jmharvey1/ESP32BtCWKeyBrd/src/bt_keyboard.cpp

// Copyright (c) 2020 Guy Turcotte
//
// MIT License. Look at file licenses.txt for details.
//
// -----
//
// Original code from the bluetooth/esp_hid_host example of ESP-IDF license:
//
// Copyright 2017-2019 Espressif Systems (Shanghai) PTE LTD
//
// Licensed under the Apache License, Version 2.0 (the "License");
// you may not use this file except in compliance with the License.
// You may obtain a copy of the License at

//     http://www.apache.org/licenses/LICENSE-2.0
//
// Unless required by applicable law or agreed to in writing, software
// distributed under the License is distributed on an "AS IS" BASIS,
// WITHOUT WARRANTIES OR CONDITIONS OF ANY KIND, either express or implied.
// See the License for the specific language governing permissions and
// limitations under the License.
/*20230503 JMH Numerous mods to adapt the original code to work with thw ESP32 BT CW Keyboard applications*/
/*20230507 JMH reversed 'TAB & TAB+Shift Assignments to make settings screen selection move in a 'Logical' order*/
/*20230721 Fixed Crash issue related to BT Keyboard sending corrupted keystroke data; fix mostly containg bt_keyboard.hid callback code*/
/*20230810 beta fix for crash linked to 1st time connection to previously 'paired keyboard. Requires stopping ADC sampling during the 'open' Keyboard event*/
/*20230811 added bt_keyboard->Adc_Sw & bt_keyboard->OpnEvntFlg params to manage ADC sampling during connecting to a previously 'paired' keyboard*/
/*20251006 reworked keyboard pairing & reconnect */
#define __BT_KEYBOARD__ 1
#include "bt_keyboard.hpp"

#include <cstring>
#include <iostream> //JMH added
#include <stdio.h>  //JMH added
#include <string.h> //JMH added
#include "esp_hidh_api.h"  //JMH added 20251005
#define SCAN 1

// uncomment to print all devices that were seen during a scan
#define GAP_DBG_PRINTF(...) printf(__VA_ARGS__)

#define SIZEOF_ARRAY(a) (sizeof(a) / sizeof(*a))

#define WAIT_BT_CB() xSemaphoreTake(bt_hidh_cb_semaphore, portMAX_DELAY)
#define SEND_BT_CB() xSemaphoreGive(bt_hidh_cb_semaphore)

#define WAIT_BLE_CB() xSemaphoreTake(ble_hidh_cb_semaphore, portMAX_DELAY)
#define SEND_BLE_CB() xSemaphoreGive(ble_hidh_cb_semaphore)
/*JMH 20230205 - replaced the following 2 lines xSemaphoreHandle with SemaphoreHandle_t */

SemaphoreHandle_t BTKeyboard::bt_hidh_cb_semaphore = nullptr;
SemaphoreHandle_t BTKeyboard::ble_hidh_cb_semaphore = nullptr;

const char *BTKeyboard::gap_bt_prop_type_names[] = {"", "BDNAME", "COD", "RSSI", "EIR"};
//const char *BTKeyboard::ble_gap_evt_names[] = {"ADV_DATA_SET_COMPLETE", "SCAN_RSP_DATA_SET_COMPLETE", "SCAN_PARAM_SET_COMPLETE", "SCAN_RESULT", "ADV_DATA_RAW_SET_COMPLETE", "SCAN_RSP_DATA_RAW_SET_COMPLETE", "ADV_START_COMPLETE", "SCAN_START_COMPLETE", "AUTH_CMPL", "KEY", "SEC_REQ", "PASSKEY_NOTIF", "PASSKEY_REQ", "OOB_REQ", "LOCAL_IR", "LOCAL_ER", "NC_REQ", "ADV_STOP_COMPLETE", "SCAN_STOP_COMPLETE", "SET_STATIC_RAND_ADDR", "UPDATE_CONN_PARAMS", "SET_PKT_LENGTH_COMPLETE", "SET_LOCAL_PRIVACY_COMPLETE", "REMOVE_BOND_DEV_COMPLETE", "CLEAR_BOND_DEV_COMPLETE", "GET_BOND_DEV_COMPLETE", "READ_RSSI_COMPLETE", "UPDATE_WHITELIST_COMPLETE"};
//const char *BTKeyboard::bt_gap_evt_names[] = {"DISC_RES", "DISC_STATE_CHANGED", "RMT_SRVCS", "RMT_SRVC_REC", "AUTH_CMPL", "PIN_REQ", "CFM_REQ", "KEY_NOTIF", "KEY_REQ", "READ_RSSI_DELTA"};
/*20251002 JMH Revised lists */
const char *BTKeyboard::bt_gap_evt_names[] = {"BT_DISC_RES",
"BT_DISC_STATE_CHANGED",
"BT_RMT_SRVCS",
"BT_RMT_SRVC_REC",
"BT_AUTH_CMPL",
"BT_PIN_REQ",
"BT_CFM_REQ",
"BT_KEY_NOTIF",
"BT_KEY_REQ",
"BT_READ_RSSI_DELTA",
"BT_CONFIG_EIR_DATA",
"BT_SET_AFH_CHANNELS",
"BT_READ_REMOTE_NAME",
"BT_MODE_CHG",
"BT_REMOVE_BOND_DEV_COMPLETE",
"BT_QOS_CMPL",
"BT_ACL_CONN_CMPL_STAT",
"BT_ACL_DISCONN_CMPL_STAT",
"BT_SET_PAGE_TO",
"BT_GET_PAGE_TO",
"BT_ACL_PKT_TYPE_CHANGED",
"BT_ENC_CHG",
"BT_GET_DEV_NAME_CMPL",
"BT_EVT_MAX"};

const char *BTKeyboard::ble_gap_evt_names[] = {"BT_DISC_RES",
"BLE_ADV_DATA_SET_COMPLETE",
"BLE_SCAN_RSP_DATA_SET_COMPLETE",
"BLE_SCAN_PARAM_SET_COMPLETE",
"BLE_SCAN_RESULT",
"BLE_ADV_DATA_RAW_SET_COMPLETE",
"BLE_SCAN_RSP_DATA_RAW_SET_COMPLETE",
"BLE_ADV_START_COMPLETE",
"BLE_SCAN_START_COMPLETE",
"BLE_AUTH_CMPL",
"BLE_KEY",
"BLE_SEC_REQ",
"BLE_PASSKEY_NOTIF",
"BLE_PASSKEY_REQ",
"BLE_OOB_REQ",
"BLE_LOCAL_IR",
"BLE_LOCAL_ER",
"BLE_NC_REQ",
"BLE_ADV_STOP_COMPLETE",
"BLE_SCAN_STOP_COMPLETE",
"BLE_SET_STATIC_RAND_ADDR",
"BLE_UPDATE_CONN_PARAMS",
"BLE_SET_PKT_LENGTH_COMPLETE",
"BLE_SET_LOCAL_PRIVACY_COMPLETE",
"BLE_REMOVE_BOND_DEV_COMPLETE",
"BLE_CLEAR_BOND_DEV_COMPLETE",
"BLE_GET_BOND_DEV_COMPLETE",
"BLE_READ_RSSI_COMPLETE",
"BLE_UPDATE_WHITELIST_COMPLETE",
"BLE_UPDATE_DUPLICATE_EXCEPTIONAL_LIST_COMPLETE",
"BLE_SET_CHANNELS",
"BLE_READ_PHY_COMPLETE",
"BLE_SET_PREFERRED_DEFAULT_PHY_COMPLETE",
"BLE_SET_PREFERRED_PHY_COMPLETE",
"BLE_EXT_ADV_SET_RAND_ADDR_COMPLETE",
"BLE_EXT_ADV_SET_PARAMS_COMPLETE",
"BLE_EXT_ADV_DATA_SET_COMPLETE",
"BLE_EXT_SCAN_RSP_DATA_SET_COMPLETE",
"BLE_EXT_ADV_START_COMPLETE",
"BLE_EXT_ADV_STOP_COMPLETE",
"BLE_EXT_ADV_SET_REMOVE_COMPLETE",
"BLE_EXT_ADV_SET_CLEAR_COMPLETE",
"BLE_PERIODIC_ADV_SET_PARAMS_COMPLETE",
"BLE_PERIODIC_ADV_DATA_SET_COMPLETE",
"BLE_PERIODIC_ADV_START_COMPLETE",
"BLE_PERIODIC_ADV_STOP_COMPLETE",
"BLE_PERIODIC_ADV_CREATE_SYNC_COMPLETE",
"BLE_PERIODIC_ADV_SYNC_CANCEL_COMPLETE",
"BLE_PERIODIC_ADV_SYNC_TERMINATE_COMPLETE",
"BLE_PERIODIC_ADV_ADD_DEV_COMPLETE",
"BLE_PERIODIC_ADV_REMOVE_DEV_COMPLETE",
"BLE_PERIODIC_ADV_CLEAR_DEV_COMPLETE",
"BLE_SET_EXT_SCAN_PARAMS_COMPLETE",
"BLE_EXT_SCAN_START_COMPLETE",
"BLE_EXT_SCAN_STOP_COMPLETE",
"BLE_PREFER_EXT_CONN_PARAMS_SET_COMPLETE",
"BLE_PHY_UPDATE_COMPLETE",
"BLE_EXT_ADV_REPORT",
"BLE_SCAN_TIMEOUT",
"BLE_ADV_TERMINATED",
"BLE_SCAN_REQ_RECEIVED",
"BLE_CHANNEL_SELECT_ALGORITHM",
"BLE_PERIODIC_ADV_REPORT",
"BLE_PERIODIC_ADV_SYNC_LOST",
"BLE_PERIODIC_ADV_SYNC_ESTAB",
"BLE_SC_OOB_REQ",
"BLE_SC_CR_LOC_OOB",
"BLE_GET_DEV_NAME_COMPLETE",
"BLE_PERIODIC_ADV_RECV_ENABLE_COMPLETE",
"BLE_PERIODIC_ADV_SYNC_TRANS_COMPLETE",
"BLE_PERIODIC_ADV_SET_INFO_TRANS_COMPLETE",
"BLE_SET_PAST_PARAMS_COMPLETE",
"BLE_PERIODIC_ADV_SYNC_TRANS_RECV",
"BLE_DTM_TEST_UPDATE",
"BLE_ADV_CLEAR_COMPLETE",
"BLE_VENDOR_CMD_COMPLETE",
"BLE_EVT_MAX"};

const char *BTKeyboard::ble_addr_type_names[] = {"PUBLIC", "RANDOM", "RPA_PUBLIC", "RPA_RANDOM"};

const char BTKeyboard::shift_trans_dict[] =
    "aAbBcCdDeEfFgGhHiIjJkKlLmMnNoOpPqQrRsStTuUvVwWxXyYzZ1!2@3#4$5%6^7&8*9(0)"
    "\r\231\033\033\b\b\t\t  -_=+[{]}\\|??;:'\"`~,<.>/?"
    "\200\200"                                          // CAPS LOC
    "\201\201\202\202\203\203\204\204\205\205\206\206"  // F1..F6
    "\207\207\210\210\211\211\212\212\213\213\214\214"  // F7..F12
    "\215\215\216\216\217\217"                          // PrintScreen ScrollLock Pause
    "\220\220\221\221\222\222\177\177"                  // Insert Home PageUp Delete
    "\223\223\224\224\225\225\226\226\227\227\230\230"; // End PageDown Right Left Dow Up

static BTKeyboard *bt_keyboard = nullptr;
static esp_hidh_dev_t *dev = nullptr;

char msgbuf[256];

void BTKeyboard::TFTmsg(const char *msg, uint16_t color)
{
  if (bt_keyboard != nullptr)
  {
    pmsgbx->dispMsg((char *)msg, color);
  }
}
const char *
BTKeyboard::ble_addr_type_str(esp_ble_addr_type_t ble_addr_type)
{
  if (ble_addr_type > BLE_ADDR_TYPE_RPA_RANDOM)
  {
    return "UNKNOWN";
  }
  return ble_addr_type_names[ble_addr_type];
}

const char *
BTKeyboard::ble_gap_evt_str(uint8_t event)
{
  if (event >= SIZEOF_ARRAY(ble_gap_evt_names))
  {
    return "UNKNOWN";
  }
  return ble_gap_evt_names[event];
}

const char *
BTKeyboard::bt_gap_evt_str(uint8_t event)
{
  if (event >= SIZEOF_ARRAY(bt_gap_evt_names))
  {
    return "UNKNOWN";
  }
  return bt_gap_evt_names[event];
}

const char *
BTKeyboard::ble_key_type_str(esp_ble_key_type_t key_type)
{
  const char *key_str = nullptr;
  switch (key_type)
  {
  case ESP_LE_KEY_NONE:
    key_str = "ESP_LE_KEY_NONE";
    break;
  case ESP_LE_KEY_PENC:
    key_str = "ESP_LE_KEY_PENC";
    break;
  case ESP_LE_KEY_PID:
    key_str = "ESP_LE_KEY_PID";
    break;
  case ESP_LE_KEY_PCSRK:
    key_str = "ESP_LE_KEY_PCSRK";
    break;
  case ESP_LE_KEY_PLK:
    key_str = "ESP_LE_KEY_PLK";
    break;
  case ESP_LE_KEY_LLK:
    key_str = "ESP_LE_KEY_LLK";
    break;
  case ESP_LE_KEY_LENC:
    key_str = "ESP_LE_KEY_LENC";
    break;
  case ESP_LE_KEY_LID:
    key_str = "ESP_LE_KEY_LID";
    break;
  case ESP_LE_KEY_LCSRK:
    key_str = "ESP_LE_KEY_LCSRK";
    break;
  default:
    key_str = "INVALID BLE KEY TYPE";
    break;
  }

  return key_str;
}

void BTKeyboard::print_uuid(esp_bt_uuid_t *uuid)
{
  if (uuid->len == ESP_UUID_LEN_16)
  {
    GAP_DBG_PRINTF("UUID16: 0x%04x", uuid->uuid.uuid16);

    if (pDFault->DeBug)
    {
      sprintf(msgbuf, "UUID16: 0x%04x ", uuid->uuid.uuid16);
      pmsgbx->dispMsg(msgbuf, TFT_WHITE);
    }
  }
  else if (uuid->len == ESP_UUID_LEN_32)
  {
    // GAP_DBG_PRINTF("UUID32: 0x%08x", uuid->uuid.uuid32);
    /*JMH 20230205 changed to solve complie error*/
    GAP_DBG_PRINTF("UUID32: 0x%08x", (unsigned int)uuid->uuid.uuid32);
    if (pDFault->DeBug)
    {
      sprintf(msgbuf, "UUID32: 0x%08x\n", (unsigned int)uuid->uuid.uuid32);
      pmsgbx->dispMsg(msgbuf, TFT_WHITE);
    }
  }
  else if (uuid->len == ESP_UUID_LEN_128)
  {
    GAP_DBG_PRINTF("UUID128: %02x,%02x,%02x,%02x,%02x,%02x,%02x,%02x,%02x,%02x,%02x,%02x,%02x,%02x,%02x,%02x",
                   uuid->uuid.uuid128[0],
                   uuid->uuid.uuid128[1], uuid->uuid.uuid128[2], uuid->uuid.uuid128[3],
                   uuid->uuid.uuid128[4], uuid->uuid.uuid128[5], uuid->uuid.uuid128[6],
                   uuid->uuid.uuid128[7], uuid->uuid.uuid128[8], uuid->uuid.uuid128[9],
                   uuid->uuid.uuid128[10], uuid->uuid.uuid128[11], uuid->uuid.uuid128[12],
                   uuid->uuid.uuid128[13], uuid->uuid.uuid128[14], uuid->uuid.uuid128[15]);
    if (pDFault->DeBug)
    {
      sprintf(msgbuf, "\nUUID128: %02x,%02x,%02x,%02x,%02x,%02x,%02x,%02x,%02x,%02x,%02x,%02x,%02x,%02x,%02x,%02x",
              uuid->uuid.uuid128[0],
              uuid->uuid.uuid128[1], uuid->uuid.uuid128[2], uuid->uuid.uuid128[3],
              uuid->uuid.uuid128[4], uuid->uuid.uuid128[5], uuid->uuid.uuid128[6],
              uuid->uuid.uuid128[7], uuid->uuid.uuid128[8], uuid->uuid.uuid128[9],
              uuid->uuid.uuid128[10], uuid->uuid.uuid128[11], uuid->uuid.uuid128[12],
              uuid->uuid.uuid128[13], uuid->uuid.uuid128[14], uuid->uuid.uuid128[15]);
      pmsgbx->dispMsg(msgbuf, TFT_WHITE);
    }
  }
}

void BTKeyboard::esp_hid_scan_results_free(esp_hid_scan_result_t *results)
{
  esp_hid_scan_result_t *r = nullptr;
  while (results)
  {
    r = results;
    results = results->next;
    if (r->name != nullptr)
    {
      free((char *)r->name);
    }
    free(r);
  }
}

BTKeyboard::esp_hid_scan_result_t *
BTKeyboard::find_scan_result(esp_bd_addr_t bda, esp_hid_scan_result_t *results)
{
  esp_hid_scan_result_t *r = results;
  while (r)
  {
    if (memcmp(bda, r->bda, sizeof(esp_bd_addr_t)) == 0)
    {
      return r;
    }
    r = r->next;
  }
  return nullptr;
}

void BTKeyboard::add_bt_scan_result(esp_bd_addr_t bda,
                                    esp_bt_cod_t *cod,
                                    esp_bt_uuid_t *uuid,
                                    uint8_t *name,
                                    uint8_t name_len,
                                    int rssi)
{
  esp_hid_scan_result_t *r = find_scan_result(bda, bt_scan_results);
  if (r)
  {
    // Some info may come later
    if (r->name == nullptr && name && name_len)
    {
      char *name_s = (char *)malloc(name_len + 1);
      if (name_s == nullptr)
      {
        ESP_LOGE(TAG, "Malloc result name failed!");
        return;
      }
      memcpy(name_s, name, name_len);
      name_s[name_len] = 0;
      r->name = (const char *)name_s;
      printf("BT New name: %s\n", r->name); //JMH Diagnostic testing
    }
    if (r->bt.uuid.len == 0 && uuid->len)
    {
      memcpy(&r->bt.uuid, uuid, sizeof(esp_bt_uuid_t));
    }
    if (rssi != 0)
    {
      r->rssi = rssi;
    }
    return;
  }

  r = (esp_hid_scan_result_t *)malloc(sizeof(esp_hid_scan_result_t));

  if (r == nullptr)
  {
    ESP_LOGE(TAG, "Malloc bt_hidh_scan_result_t failed!");
    if (pDFault->DeBug)
    {
      sprintf(msgbuf, "Malloc bt_hidh_scan_result_t failed!\n");
      pmsgbx->dispMsg(msgbuf, TFT_RED);
    }
    return;
  }

  r->transport = ESP_HID_TRANSPORT_BT;

  memcpy(r->bda, bda, sizeof(esp_bd_addr_t));
  memcpy(&r->bt.cod, cod, sizeof(esp_bt_cod_t));
  memcpy(&r->bt.uuid, uuid, sizeof(esp_bt_uuid_t));

  r->usage = esp_hid_usage_from_cod((uint32_t)cod);
  r->rssi = rssi;
  r->name = nullptr;

  if (name_len && name)
  {
    char *name_s = (char *)malloc(name_len + 1);
    if (name_s == nullptr)
    {
      free(r);
      ESP_LOGE(TAG, "Malloc result name failed!");
      if (pDFault->DeBug)
      {
        sprintf(msgbuf, "Malloc result name failed!\n");
        pmsgbx->dispMsg(msgbuf, TFT_RED);
      }
      return;
    }
    memcpy(name_s, name, name_len);
    name_s[name_len] = 0;
    r->name = (const char *)name_s;
  }
  r->next = bt_scan_results;
  bt_scan_results = r;
  num_bt_scan_results++;
}

void BTKeyboard::add_ble_scan_result(esp_bd_addr_t bda,
                                     esp_ble_addr_type_t addr_type,
                                     uint16_t appearance,
                                     uint8_t *name,
                                     uint8_t name_len,
                                     int rssi)
{
  if (find_scan_result(bda, ble_scan_results))
  {
    ESP_LOGW(TAG, "Result already exists!");
    if (pDFault->DeBug)
    {
      sprintf(msgbuf, "Result already exists!\n");
      pmsgbx->dispMsg(msgbuf, TFT_YELLOW);
    }
    return;
  }

  esp_hid_scan_result_t *r = (esp_hid_scan_result_t *)malloc(sizeof(esp_hid_scan_result_t));

  if (r == nullptr)
  {
    ESP_LOGE(TAG, "Malloc ble_hidh_scan_result_t failed!");
    if (pDFault->DeBug)
    {
      sprintf(msgbuf, "Malloc ble_hidh_scan_result_t failed!\n");
      pmsgbx->dispMsg(msgbuf, TFT_RED);
    }
    return;
  }

  r->transport = ESP_HID_TRANSPORT_BLE;

  memcpy(r->bda, bda, sizeof(esp_bd_addr_t));

  r->ble.appearance = appearance;
  r->ble.addr_type = addr_type;
  r->usage = esp_hid_usage_from_appearance(appearance);
  r->rssi = rssi;
  r->name = nullptr;

  if (name_len && name)
  {
    char *name_s = (char *)malloc(name_len + 1);
    if (name_s == nullptr)
    {
      free(r);
      ESP_LOGE(TAG, "Malloc result name failed!");
      if (pDFault->DeBug)
      {
        sprintf(msgbuf, "Malloc result name failed!\n");
        pmsgbx->dispMsg(msgbuf, TFT_RED);
      }
      return;
    }
    memcpy(name_s, name, name_len);
    name_s[name_len] = 0;
    r->name = (const char *)name_s;
    printf("BLE New name: %s\n", r->name); //JMH Diagnostic testing
  }

  r->next = ble_scan_results;
  ble_scan_results = r;
  num_ble_scan_results++;
}

bool BTKeyboard::setup(pid_handler *handler)
{
  esp_err_t ret;
  const esp_bt_mode_t mode = HID_HOST_MODE;

  if (bt_keyboard != nullptr)
  {
    ESP_LOGE(TAG, "Setup called more than once. Only one instance of BTKeyboard is allowed.");
    if (pDFault->DeBug)
    {
      sprintf(msgbuf, "Setup called more than once. Only one instance of BTKeyboard is allowed.\n");
      pmsgbx->dispMsg(msgbuf, TFT_YELLOW);
    }
    return false;
  }

  bt_keyboard = this;

  pairing_handler = handler;
  event_queue = xQueueCreate(10, sizeof(KeyInfo));

  if (HID_HOST_MODE == HIDH_IDLE_MODE)
  {
    ESP_LOGE(TAG, "Please turn on BT HID host or BLE!");
    sprintf(msgbuf, "Please turn on BT HID host or BLE!\n");
    pmsgbx->dispStat(msgbuf, TFT_YELLOW);
    return false;
  }

  bt_hidh_cb_semaphore = xSemaphoreCreateBinary();
  if (bt_hidh_cb_semaphore == nullptr)
  {
    ESP_LOGE(TAG, "xSemaphoreCreateMutex failed!");
    sprintf(msgbuf, "xSemaphoreCreateMutex failed!\n");
    pmsgbx->dispStat(msgbuf, TFT_RED);
    return false;
  }

  ble_hidh_cb_semaphore = xSemaphoreCreateBinary();
  if (ble_hidh_cb_semaphore == nullptr)
  {
    ESP_LOGE(TAG, "xSemaphoreCreateMutex failed!");
    sprintf(msgbuf, "xSemaphoreCreateMutex failed!\n");
    pmsgbx->dispStat(msgbuf, TFT_RED);
    vSemaphoreDelete(bt_hidh_cb_semaphore);
    bt_hidh_cb_semaphore = nullptr;
    return false;
  }

  esp_bt_controller_config_t bt_cfg = BT_CONTROLLER_INIT_CONFIG_DEFAULT();

  bt_cfg.mode = mode;
  bt_cfg.bt_max_acl_conn = 3;
  bt_cfg.bt_max_sync_conn = 3;

  if ((ret = esp_bt_controller_init(&bt_cfg)))
  {
    ESP_LOGE(TAG, "esp_bt_controller_init failed: %d", ret);
    sprintf(msgbuf, "esp_bt_controller_init failed: %d\n", ret);
    pmsgbx->dispStat(msgbuf, TFT_YELLOW);
    return false;
  }

  if ((ret = esp_bt_controller_enable(mode)))
  {
    ESP_LOGE(TAG, "esp_bt_controller_enable failed: %d", ret);
    sprintf(msgbuf, "esp_bt_controller_enable failed: %d\n", ret);
    pmsgbx->dispStat(msgbuf, TFT_YELLOW);
    return false;
  }

  if ((ret = esp_bluedroid_init()))
  {
    ESP_LOGE(TAG, "esp_bluedroid_init failed: %d", ret);
    sprintf(msgbuf, "esp_bluedroid_init failed: %d\n", ret);
    pmsgbx->dispStat(msgbuf, TFT_YELLOW);
    return false;
  }

  if ((ret = esp_bluedroid_enable()))
  {
    ESP_LOGE(TAG, "esp_bluedroid_enable failed: %d", ret);
    sprintf(msgbuf, "esp_bluedroid_enable failed: %d\n", ret);
    pmsgbx->dispStat(msgbuf, TFT_YELLOW);
    return false;
  }

  // Classic Bluetooth GAP

  esp_bt_sp_param_t param_type = ESP_BT_SP_IOCAP_MODE;
  //esp_bt_io_cap_t iocap = ESP_BT_IO_CAP_IO;
  esp_bt_gap_set_security_param(param_type, &iocap, sizeof(uint8_t));

  /*
   * Set default parameters for Legacy Pairing
   * Use variable pin, input pin code when pairing
   */
  esp_bt_pin_type_t pin_type = ESP_BT_PIN_TYPE_VARIABLE;
  esp_bt_pin_code_t pin_code;
  esp_bt_gap_set_pin(pin_type, 0, pin_code);

  if ((ret = esp_bt_gap_register_callback(bt_gap_event_handler)))
  {
    ESP_LOGE(TAG, "esp_bt_gap_register_callback failed: %d", ret);
    sprintf(msgbuf, "esp_bt_gap_register_callback failed: %d\n", ret);
    pmsgbx->dispStat(msgbuf, TFT_YELLOW);
    return false;
  }

  // Allow BT devices to connect back to us
  if ((ret = esp_bt_gap_set_scan_mode(ESP_BT_CONNECTABLE, ESP_BT_NON_DISCOVERABLE)))
  {
    ESP_LOGE(TAG, "esp_bt_gap_set_scan_mode failed: %d", ret);
    sprintf(msgbuf, "esp_bt_gap_set_scan_mode failed: %d\n", ret);
    pmsgbx->dispStat(msgbuf, TFT_YELLOW);
    return false;
  }

  // BLE GAP

  if ((ret = esp_ble_gap_register_callback(ble_gap_event_handler)))
  {
    ESP_LOGE(TAG, "esp_ble_gap_register_callback failed: %d", ret);
    sprintf(msgbuf, "esp_bt_gap_set_scan_mode ffailed: %d\n", ret);
    pmsgbx->dispStat(msgbuf, TFT_YELLOW);
    return false;
  }

  ESP_ERROR_CHECK(esp_ble_gattc_register_callback(esp_hidh_gattc_event_handler));
  esp_hidh_config_t config = {
      .callback = hidh_callback,
      .event_stack_size = 4 * 1024, // Required with ESP-IDF 4.4
      .callback_arg = nullptr       // idem
  };
  ESP_ERROR_CHECK(esp_hidh_init(&config));

  for (int i = 0; i < MAX_KEY_COUNT; i++)
  {
    key_avail[i] = true;
  }
  last_ch = 0;
  battery_level = -1;
  return true;
}

void BTKeyboard::handle_bt_device_result(esp_bt_gap_cb_param_t *param)
{
  GAP_DBG_PRINTF("BT : " ESP_BD_ADDR_STR, ESP_BD_ADDR_HEX(param->disc_res.bda));
  if (pDFault->DeBug)
  {
    sprintf(msgbuf, "BT  %02x:%02x:%02x:%02x:%02x:%02x", ESP_BD_ADDR_HEX(param->disc_res.bda));
    pmsgbx->dispMsg(msgbuf, TFT_WHITE);
  }
  uint32_t codv = 0;
  esp_bt_cod_t *cod = (esp_bt_cod_t *)&codv;
  int8_t rssi = 0;
  uint8_t *name = nullptr;
  uint8_t name_len = 0;
  esp_bt_uuid_t uuid;

  uuid.len = ESP_UUID_LEN_16;
  uuid.uuid.uuid16 = 0;

  for (int i = 0; i < param->disc_res.num_prop; i++)
  {
    esp_bt_gap_dev_prop_t *prop = &param->disc_res.prop[i];
    if (prop->type != ESP_BT_GAP_DEV_PROP_EIR)
    {
      GAP_DBG_PRINTF(", %s: ", gap_bt_prop_type_names[prop->type]);
      // if (pDFault->DeBug)
      // {
      //   sprintf(msgbuf, ", %s: ", gap_bt_prop_type_names[prop->type]);
      //   pmsgbx->dispMsg(msgbuf, TFT_WHITE);
      // }
    }
    if (prop->type == ESP_BT_GAP_DEV_PROP_BDNAME)
    {
      name = (uint8_t *)prop->val;
      name_len = strlen((const char *)name);
      GAP_DBG_PRINTF("%s", (const char *)name);
      if (pDFault->DeBug)
      {
        sprintf(msgbuf, "%s", (const char *)name);
        pmsgbx->dispMsg(msgbuf, TFT_WHITE);
      }
    }
    else if (prop->type == ESP_BT_GAP_DEV_PROP_RSSI)
    {
      rssi = *((int8_t *)prop->val);
      GAP_DBG_PRINTF("%d", rssi);
      // if (pDFault->DeBug)
      // {
      //   sprintf(msgbuf, "%d", rssi);
      //   pmsgbx->dispMsg(msgbuf, TFT_WHITE);
      // }
    }
    else if (prop->type == ESP_BT_GAP_DEV_PROP_COD)
    {
      memcpy(&codv, prop->val, sizeof(uint32_t));
      GAP_DBG_PRINTF("major: %s, minor: %d, service: 0x%03x", esp_hid_cod_major_str(cod->major), cod->minor, cod->service);
      // if (pDFault->DeBug)
      // {
      //   sprintf(msgbuf, "major: %s, minor: %d, service: 0x%03x", esp_hid_cod_major_str(cod->major), cod->minor, cod->service);
      //   pmsgbx->dispMsg(msgbuf, TFT_WHITE);
      // }
    }
    else if (prop->type == ESP_BT_GAP_DEV_PROP_EIR)
    {
      uint8_t len = 0;
      uint8_t *data = 0;

      data = esp_bt_gap_resolve_eir_data((uint8_t *)prop->val, ESP_BT_EIR_TYPE_CMPL_16BITS_UUID, &len);

      if (data == nullptr)
      {
        data = esp_bt_gap_resolve_eir_data((uint8_t *)prop->val, ESP_BT_EIR_TYPE_INCMPL_16BITS_UUID, &len);
      }

      if (data && len == ESP_UUID_LEN_16)
      {
        uuid.len = ESP_UUID_LEN_16;
        uuid.uuid.uuid16 = data[0] + (data[1] << 8);
        GAP_DBG_PRINTF(", ");
        print_uuid(&uuid);
        continue;
      }

      data = esp_bt_gap_resolve_eir_data((uint8_t *)prop->val, ESP_BT_EIR_TYPE_CMPL_32BITS_UUID, &len);

      if (data == nullptr)
      {
        data = esp_bt_gap_resolve_eir_data((uint8_t *)prop->val, ESP_BT_EIR_TYPE_INCMPL_32BITS_UUID, &len);
      }

      if (data && len == ESP_UUID_LEN_32)
      {
        uuid.len = len;
        memcpy(&uuid.uuid.uuid32, data, sizeof(uint32_t));
        GAP_DBG_PRINTF(", ");
        print_uuid(&uuid);
        continue;
      }

      data = esp_bt_gap_resolve_eir_data((uint8_t *)prop->val, ESP_BT_EIR_TYPE_CMPL_128BITS_UUID, &len);

      if (data == nullptr)
      {
        data = esp_bt_gap_resolve_eir_data((uint8_t *)prop->val, ESP_BT_EIR_TYPE_INCMPL_128BITS_UUID, &len);
      }

      if (data && len == ESP_UUID_LEN_128)
      {
        uuid.len = len;
        memcpy(uuid.uuid.uuid128, (uint8_t *)data, len);
        GAP_DBG_PRINTF(", ");
        print_uuid(&uuid);
        continue;
      }

      // try to find a name
      if (name == nullptr)
      {
        data = esp_bt_gap_resolve_eir_data((uint8_t *)prop->val, ESP_BT_EIR_TYPE_CMPL_LOCAL_NAME, &len);

        if (data == nullptr)
        {
          data = esp_bt_gap_resolve_eir_data((uint8_t *)prop->val, ESP_BT_EIR_TYPE_SHORT_LOCAL_NAME, &len);
        }

        if (data && len)
        {
          name = data;
          name_len = len;
          GAP_DBG_PRINTF(", NAME: ");
          if (pDFault->DeBug)
          {
            sprintf(msgbuf, ", ");
            for (int x = 0; x < len; x++)
            {
              GAP_DBG_PRINTF("%c", (char)data[x]);
              /*inspite of the given lenght, treat every entry as if it were one & terminate the array with LF & 0*/
              msgbuf[2 + x] = (char)data[x];
              // msgbuf[2 + x + 1] = 0xA; // lf
              // msgbuf[2 + x + 2] = 0;
              msgbuf[2 + x + 1] = 0;
            }
            pmsgbx->dispMsg(msgbuf, TFT_WHITE);
          }
        }
      }
    }
  }
  GAP_DBG_PRINTF("\n");
  if (pDFault->DeBug)
  {
    sprintf(msgbuf, "\n");
    pmsgbx->dispMsg(msgbuf, TFT_WHITE);
  }

  if ((cod->major == ESP_BT_COD_MAJOR_DEV_PERIPHERAL) ||
      (find_scan_result(param->disc_res.bda, bt_scan_results) != nullptr))
  {
    add_bt_scan_result(param->disc_res.bda, cod, &uuid, name, name_len, rssi);
  }
}

void BTKeyboard::bt_gap_event_handler(esp_bt_gap_cb_event_t event, esp_bt_gap_cb_param_t *param)
{
  static const char *TAG1 = "bt_gap_event_handler";
  GAP_DBG_PRINTF("\tBT GAP EVT: (%d) %s\n", event, bt_gap_evt_str(event));
  switch (event)
  {
    
  case ESP_BT_GAP_DISC_STATE_CHANGED_EVT:
  {
    ESP_LOGV(TAG, "BT GAP DISC_STATE %s", (param->disc_st_chg.state == ESP_BT_GAP_DISCOVERY_STARTED) ? "START" : "STOP");
    // if(pDFault->DeBug){
    //sprintf(msgbuf, "BT GAP DISC_STATE %s", (param->disc_st_chg.state == ESP_BT_GAP_DISCOVERY_STARTED) ? "START" : "STOP"); //JMH Diagnosstic testing
    //   pmsgbx->dispMsg(msgbuf,TFT_WHITE);
    // }
    if (param->disc_st_chg.state == ESP_BT_GAP_DISCOVERY_STOPPED)
    {
      SEND_BT_CB();
    }
    break;
  }
  case ESP_BT_GAP_DISC_RES_EVT:
  {
    bt_keyboard->handle_bt_device_result(param);
    break;
  }
  case ESP_BT_GAP_AUTH_CMPL_EVT:                         /*!< Authentication complete indication */
  {
    if (param->auth_cmpl.stat == ESP_BT_STATUS_SUCCESS)
    {
      ESP_LOGI(TAG, "BT GAP AUTH_CMPL name:%s", param->auth_cmpl.device_name);
      // if(pDFault->DeBug){
      // sprintf(msgbuf, "BT GAP AUTH_CMPL name:%s", param->auth_cmpl.device_name); //JMH Diagnosstic testing
      // printf("bt_gap_event_handler: %s \n",msgbuf); //JMH Diagnosstic testing
      //   pmsgbx->dispMsg(msgbuf,TFT_WHITE);
      // }
      ESP_LOGI(TAG, "BT GAP AUTH_CMPL address:%02x:%02x:%02x:%02x:%02x:%02x",
               param->auth_cmpl.bda[0], param->auth_cmpl.bda[1], param->auth_cmpl.bda[2],
               param->auth_cmpl.bda[3], param->auth_cmpl.bda[4], param->auth_cmpl.bda[5]);
      // if(pDFault->DeBug){
      sprintf(msgbuf, "BT GAP AUTH_CMPL address:%02x:%02x:%02x:%02x:%02x:%02x",
              param->auth_cmpl.bda[0], param->auth_cmpl.bda[1], param->auth_cmpl.bda[2],
              param->auth_cmpl.bda[3], param->auth_cmpl.bda[4], param->auth_cmpl.bda[5]); //JMH Diagnosstic testing
      printf("bt_gap_event_handler: %s \n",msgbuf); //JMH Diagnosstic testing
      //   pmsgbx->dispMsg(msgbuf,TFT_WHITE);
      // }
    }
    else
    {
      ESP_LOGE(TAG, "BT GAP AUTH_CMPL failed, status:%d", param->auth_cmpl.stat);
      // if(pDFault->DeBug){
      sprintf(msgbuf, "BT GAP AUTH_CMPL failed, status:%d", param->auth_cmpl.stat); //JMH Diagnosstic testing
      printf("bt_gap_event_handler: %s \n",msgbuf); //JMH Diagnosstic testing
      //   pmsgbx->dispMsg(msgbuf,TFT_RED);
    }
    break;
  }
  case ESP_BT_GAP_PIN_REQ_EVT:                            /*!< Legacy Pairing Pin code request */
  {
    ESP_LOGI(TAG, "BT GAP PIN_REQ_EVT min_16_digit:%d", param->pin_req.min_16_digit);
    if (param->pin_req.min_16_digit)
    {
      ESP_LOGI(TAG, "Input pin code: 0000 0000 0000 0000");
      sprintf(msgbuf, "Input pin code: 0000 0000 0000 0000\n");
      bt_keyboard->TFTmsg(msgbuf, TFT_WHITE);
      esp_bt_pin_code_t pin_code = {0};
      esp_bt_gap_pin_reply(param->pin_req.bda, true, 16, pin_code);
    }
    else
    {
      ESP_LOGI(TAG, "Input pin code: 1234");
      esp_bt_pin_code_t pin_code;
      pin_code[0] = '1';
      pin_code[1] = '2';
      pin_code[2] = '3';
      pin_code[3] = '4';
      if (esp_bt_gap_pin_reply(param->pin_req.bda, true, 4, pin_code))
      // if (esp_bt_gap_set_pin(pin_type, 4, pin_code))
      {
        ESP_LOGE(TAG, "esp_bt_gap_set_pin failed");
        sprintf(msgbuf, "esp_bt_gap_set_pin failed\n");
        bt_keyboard->TFTmsg(msgbuf, TFT_YELLOW);
        // pmsgbx->dispStat(msgbuf, TFT_YELLOW);
      }
      else
      {
        sprintf(msgbuf, "ENTER pairing code: 1234\n");
        // pmsgbx->dispMsg(msgbuf, TFT_WHITE);
        bt_keyboard->TFTmsg(msgbuf, TFT_WHITE);
      }
    }
    break;
  }
  case ESP_BT_GAP_CFM_REQ_EVT:                         /*!< Security Simple Pairing User Confirmation request. */
  {
    sprintf(msgbuf, "BT GAP CFM_REQ numeric_value:%lu", param->cfm_req.num_val); //JMH Diagnosstic testing
    printf("bt_gap_event_handler: %s \n",msgbuf); //JMH Diagnosstic testing
    break;
  }
  case ESP_BT_GAP_KEY_NOTIF_EVT:  /*!< Security Simple Pairing Passkey Notification */
    //ESP_LOGV(TAG, "BT GAP KEY_NOTIF passkey:%d", param->key_notif.passkey); // JMH changed %lu to %d 
    ESP_LOGV(TAG, "BT GAP KEY_NOTIF passkey:%lu", param->key_notif.passkey); // JMH changed for WINDOWS 10 version
    //   if(pDFault->DeBug){
          sprintf(msgbuf, "BT GAP KEY_NOTIF passkey:%lu", param->key_notif.passkey); //JMH Diagnosstic testing
          printf("bt_gap_event_handler: %s \n",msgbuf); //JMH Diagnosstic testing
          //pmsgbx->dispMsg(msgbuf,TFT_WHITE);
    // }
    if (bt_keyboard->pairing_handler != nullptr)
      (*bt_keyboard->pairing_handler)(param->key_notif.passkey);
    break;
  case ESP_BT_GAP_KEY_REQ_EVT:                         /*!< Security Simple Pairing Passkey request */
  {
    sprintf(msgbuf, "BT GAP KEY_REQ"); //JMH Diagnosstic testing
    printf("bt_gap_event_handler: %s \n",msgbuf); //JMH Diagnosstic testing
    break;
  }
  case ESP_BT_GAP_MODE_CHG_EVT:
    ESP_LOGV(TAG, "BT GAP MODE_CHG_EVT mode:%d", param->mode_chg.mode);
    // if(pDFault->DeBug){
    //sprintf(msgbuf, "BT GAP MODE_CHG_EVT mode:%d", param->mode_chg.mode); //JMH Diagnosstic testing
    //   pmsgbx->dispMsg(msgbuf,TFT_WHITE);
    // }

    if((param->mode_chg.mode == 0) && !bt_keyboard->OpnEvntFlg && adcON){
      ESP_LOGI(TAG1, "adc_continuous_stop");
      bt_keyboard->Adc_Sw = 1;
      vTaskDelay(20);
    }
    break;
  case ESP_BT_GAP_ACL_CONN_CMPL_STAT_EVT:
    if (param->acl_conn_cmpl_stat.stat == ESP_BT_STATUS_SUCCESS)
    {
      ESP_LOGI(TAG, "ACL connection successful");
      // The HID host API must now be called to start the SDP process.
      // An internal Bluedroid state machine usually manages this
      // based on the successful ACL connection. The callback
      // function registered via `esp_bt_hid_host_register_callback`
      // will handle the next HID-specific events (like OPEN_EVT).
      // Attempt to open a secure paired HID connection
      if (bt_keyboard->ReConectFlg)
      {
        bt_keyboard->ReConectFlg = false;
        ESP_LOGI(TAG, "Pairing in progress, skipping re-pairing.");
      }
      else
      { // Not paired yet, try to open a secure connection
        memcpy(&bt_keyboard->bd_addr, param->acl_conn_cmpl_stat.bda, sizeof(esp_bd_addr_t)); //param->acl_conn_cmpl_stat.bda;
        ESP_LOGI(TAG, "starting HID service discovery (ADC_SW = %d)", bt_keyboard->Adc_Sw );
        dev = esp_hidh_dev_open(bt_keyboard->bd_addr, ESP_HID_TRANSPORT_BT, 9536);
        if (dev != NULL)
        {
          vTaskDelay(400); // Wait a bit
          if (esp_bt_gap_set_security_param(ESP_BT_SP_IOCAP_MODE, &bt_keyboard->iocap, sizeof(esp_bt_io_cap_t)) != ESP_OK)
          {
            ESP_LOGE(TAG, "Failed to set security parameters for pairing");
          }
          else
          {
            //vTaskDelay(400); // Wait a bit for the disconnection to complete
            ESP_LOGI(TAG, "Successfully Re-opened secure HID connection to " ESP_BD_ADDR_STR, ESP_BD_ADDR_HEX(bt_keyboard->bd_addr));
          }
        }
        else
        {
          ESP_LOGE(TAG, "Failed to open secure HID connection to " ESP_BD_ADDR_STR, ESP_BD_ADDR_HEX(bt_keyboard->bd_addr));
          sprintf(msgbuf, "Failed to open secure HID connection to " ESP_BD_ADDR_STR "\n", ESP_BD_ADDR_HEX(bt_keyboard->bd_addr));
          bt_keyboard->TFTmsg(msgbuf, TFT_YELLOW);
        }
      }
    }
    else
    {
      ESP_LOGE(TAG, "ACL connection failed");
    }
    break;
  case ESP_BT_GAP_ACL_DISCONN_CMPL_STAT_EVT:
  {
    bt_keyboard->OpnEvntFlg = false;
    ESP_LOGI(TAG, "ACL disconnected");
    //sprintf(msgbuf, "ACL disconnected\n");
    //bt_keyboard->TFTmsg(msgbuf, TFT_WHITE);
    break;
  }
  default:
    ESP_LOGW(TAG, "BT GAP EVENT %s", bt_gap_evt_str(event));
    break;
  }
  //printf("bt_gap_event_handler: %s EXIT\n",msgbuf); //JMH Diagnosstic testing
}

void BTKeyboard::handle_ble_device_result(esp_ble_gap_cb_param_t *param)
{
  uint16_t uuid = 0;
  uint16_t appearance = 0;
  char name[64] = "";

  uint8_t uuid_len = 0;
  uint8_t *uuid_d = esp_ble_resolve_adv_data(param->scan_rst.ble_adv, ESP_BLE_AD_TYPE_16SRV_CMPL, &uuid_len);

  if (uuid_d != nullptr && uuid_len)
  {
    uuid = uuid_d[0] + (uuid_d[1] << 8);
  }

  uint8_t appearance_len = 0;
  uint8_t *appearance_d = esp_ble_resolve_adv_data(param->scan_rst.ble_adv, ESP_BLE_AD_TYPE_APPEARANCE, &appearance_len);

  if (appearance_d != nullptr && appearance_len)
  {
    appearance = appearance_d[0] + (appearance_d[1] << 8);
  }

  uint8_t adv_name_len = 0;
  uint8_t *adv_name = esp_ble_resolve_adv_data(param->scan_rst.ble_adv, ESP_BLE_AD_TYPE_NAME_CMPL, &adv_name_len);

  if (adv_name == nullptr)
  {
    adv_name = esp_ble_resolve_adv_data(param->scan_rst.ble_adv, ESP_BLE_AD_TYPE_NAME_SHORT, &adv_name_len);
  }

  if (adv_name != nullptr && adv_name_len)
  {
    memcpy(name, adv_name, adv_name_len);
    name[adv_name_len] = 0;
  }

  GAP_DBG_PRINTF("BLE: " ESP_BD_ADDR_STR ", ", ESP_BD_ADDR_HEX(param->scan_rst.bda));
  GAP_DBG_PRINTF("RSSI: %d, ", param->scan_rst.rssi);
  // if (pDFault->DeBug)
  // {
  //   sprintf(msgbuf, "RSSI: %d, ", param->scan_rst.rssi);
  //   pmsgbx->dispMsg(msgbuf, TFT_WHITE);
  // }
  GAP_DBG_PRINTF("UUID: 0x%04x, ", uuid);
  // if (pDFault->DeBug)
  // {
  //   sprintf(msgbuf, "UUID: 0x%04x, ", uuid);
  //   pmsgbx->dispMsg(msgbuf, TFT_WHITE);
  // }
  GAP_DBG_PRINTF("APPEARANCE: 0x%04x, ", appearance);
  // if (pDFault->DeBug)
  // {
  //   sprintf(msgbuf, "APPEARANCE: 0x%04x, ", appearance);
  //   pmsgbx->dispMsg(msgbuf, TFT_WHITE);
  // }
  GAP_DBG_PRINTF("ADDR_TYPE: '%s'", ble_addr_type_str(param->scan_rst.ble_addr_type));
  // if (pDFault->DeBug)
  // {
  //   sprintf(msgbuf, "ADDR_TYPE: '%s'", ble_addr_type_str(param->scan_rst.ble_addr_type));
  //   pmsgbx->dispMsg(msgbuf, TFT_WHITE);
  // }

  if (adv_name_len)
  {
    GAP_DBG_PRINTF(", NAME: '%s'", name);
    if (pDFault->DeBug)
    {
      sprintf(msgbuf, ", NAME: '%s'", name);
      pmsgbx->dispMsg(msgbuf, TFT_WHITE);
    }
  }
  GAP_DBG_PRINTF("\n");
  if (pDFault->DeBug)
  {
    sprintf(msgbuf, "\n");
    pmsgbx->dispMsg(msgbuf, TFT_WHITE);
  }

#if SCAN
  if (uuid == ESP_GATT_UUID_HID_SVC)
  {
    add_ble_scan_result(param->scan_rst.bda,
                        param->scan_rst.ble_addr_type,
                        appearance, adv_name, adv_name_len,
                        param->scan_rst.rssi);
  }
#endif
}

void BTKeyboard::ble_gap_event_handler(esp_gap_ble_cb_event_t event, esp_ble_gap_cb_param_t *param)
{
  static const char *TAG1 = "ble_gap_event_handler";
  //sprintf(msgbuf, "ble_gap_event_handler: %d", event); //JMH Diagnostic testing
  //printf("ble_gap_event_handler: %s \n",msgbuf); //JMH Diagnostic testing
  GAP_DBG_PRINTF("BLE GAP EVT: (%d) %s\n", event, ble_gap_evt_str(event));
  switch (event)
  {

    // SCAN

  case ESP_GAP_BLE_SCAN_PARAM_SET_COMPLETE_EVT:
  {
    ESP_LOGV(TAG, "BLE GAP EVENT SCAN_PARAM_SET_COMPLETE");
    // if(pDFault->DeBug){
    //   sprintf(msgbuf, "BLE GAP EVENT SCAN_PARAM_SET_COMPLETE");
    //   pmsgbx->dispMsg(msgbuf,TFT_WHITE);
    // }
    SEND_BLE_CB();
    break;
  }
  case ESP_GAP_BLE_SCAN_RESULT_EVT:
  {
    switch (param->scan_rst.search_evt)
    {
    case ESP_GAP_SEARCH_INQ_RES_EVT:
    {
      bt_keyboard->handle_ble_device_result(param);
      break;
    }
    case ESP_GAP_SEARCH_INQ_CMPL_EVT:
      ESP_LOGV(TAG, "BLE GAP EVENT SCAN DONE: %d", param->scan_rst.num_resps);
      // if(pDFault->DeBug){
      //   sprintf(msgbuf, "BLE GAP EVENT SCAN DONE: %d", param->scan_rst.num_resps);
      //   pmsgbx->dispMsg(msgbuf,TFT_WHITE);
      // }
      SEND_BLE_CB();
      break;
    default:
      break;
    }
    break;
  }
  case ESP_GAP_BLE_SCAN_STOP_COMPLETE_EVT:
  {
    ESP_LOGV(TAG, "BLE GAP EVENT SCAN CANCELED");
    // if(pDFault->DeBug){
    //   sprintf(msgbuf, "BLE GAP EVENT SCAN CANCELED");
    //   pmsgbx->dispMsg(msgbuf,TFT_WHITE);
    // }
    break;
  }

    // ADVERTISEMENT

  case ESP_GAP_BLE_ADV_DATA_SET_COMPLETE_EVT:
    ESP_LOGV(TAG, "BLE GAP ADV_DATA_SET_COMPLETE");
    // if(pDFault->DeBug){
    //   sprintf(msgbuf, "BLE GAP ADV_DATA_SET_COMPLETE");
    //   pmsgbx->dispMsg(msgbuf,TFT_WHITE);
    // }
    break;

  case ESP_GAP_BLE_ADV_START_COMPLETE_EVT:
    ESP_LOGV(TAG, "BLE GAP ADV_START_COMPLETE");
    // if(pDFault->DeBug){
    //   sprintf(msgbuf, "BLE GAP ADV_START_COMPLETE");
    //   pmsgbx->dispMsg(msgbuf,TFT_WHITE);
    // }
    break;

    // AUTHENTICATION

  case ESP_GAP_BLE_AUTH_CMPL_EVT:
    if (!param->ble_security.auth_cmpl.success)
    {
      ESP_LOGE(TAG, "BLE GAP AUTH ERROR: 0x%x", param->ble_security.auth_cmpl.fail_reason);
      // if(pDFault->DeBug){
      //   sprintf(msgbuf, "BLE GAP AUTH ERROR: 0x%x", param->ble_security.auth_cmpl.fail_reason);
      //   pmsgbx->dispMsg(msgbuf,TFT_RED);
      // }
    }
    else
    {
      ESP_LOGV(TAG, "BLE GAP AUTH SUCCESS");
      // if(pDFault->DeBug){
      //   sprintf(msgbuf, "BLE GAP AUTH SUCCESS");
      //   pmsgbx->dispMsg(msgbuf,TFT_GREEN);
      // }
      break;

    case ESP_GAP_BLE_KEY_EVT: // shows the ble key info share with peer device to the user.
      ESP_LOGV(TAG, "BLE GAP KEY type = %s", ble_key_type_str(param->ble_security.ble_key.key_type));
      // if(pDFault->DeBug){
      // sprintf(msgbuf, "BLE GAP KEY type = %s", ble_key_type_str(param->ble_security.ble_key.key_type));
      // pmsgbx->dispMsg(msgbuf,TFT_WHITE);
      // }
      break;

    case ESP_GAP_BLE_PASSKEY_NOTIF_EVT: // ESP_IO_CAP_OUT
      // The app will receive this evt when the IO has Output capability and the peer device IO has Input capability.
      // Show the passkey number to the user to input it in the peer device.
      //ESP_LOGV(TAG, "BLE GAP PASSKEY_NOTIF passkey:%d", param->ble_security.key_notif.passkey); // JMH changed %d to %lu
      ESP_LOGV(TAG, "BLE GAP PASSKEY_NOTIF passkey:%lu", param->ble_security.key_notif.passkey); // JMH changed %d to %lu for Windows 10 Version
      // if(pDFault->DeBug){
      //    sprintf(msgbuf, "BLE GAP PASSKEY_NOTIF passkey:%lu", param->ble_security.key_notif.passkey);
      //    pmsgbx->dispMsg(msgbuf,TFT_WHITE);
      //}
      if (bt_keyboard->pairing_handler != nullptr)
        (*bt_keyboard->pairing_handler)(param->ble_security.key_notif.passkey);
      break;

    case ESP_GAP_BLE_NC_REQ_EVT: // ESP_IO_CAP_IO
      // The app will receive this event when the IO has DisplayYesNO capability and the peer device IO also has DisplayYesNo capability.
      // show the passkey number to the user to confirm it with the number displayed by peer device.
      //ESP_LOGV(TAG, "BLE GAP NC_REQ passkey:%d", param->ble_security.key_notif.passkey); // JMH changed %d to %lu
      ESP_LOGV(TAG, "BLE GAP NC_REQ passkey:%lu", param->ble_security.key_notif.passkey); // JMH changed %d to %lu for Windows 10 version
      // if(pDFault->DeBug){
      // sprintf(msgbuf, "BLE GAP NC_REQ passkey:%lu", param->ble_security.key_notif.passkey);
      // pmsgbx->dispMsg(msgbuf,TFT_WHITE);
      //}
      esp_ble_confirm_reply(param->ble_security.key_notif.bd_addr, true);
      break;

    case ESP_GAP_BLE_PASSKEY_REQ_EVT: // ESP_IO_CAP_IN
      // The app will receive this evt when the IO has Input capability and the peer device IO has Output capability.
      // See the passkey number on the peer device and send it back.
      ESP_LOGV(TAG, "BLE GAP PASSKEY_REQ");
      // if(pDFault->DeBug){
      // sprintf(msgbuf, "BLE GAP PASSKEY_REQ");
      // pmsgbx->dispMsg(msgbuf,TFT_WHITE);
      //}
      esp_ble_passkey_reply(param->ble_security.ble_req.bd_addr, true, 1234);
      break;

    case ESP_GAP_BLE_SEC_REQ_EVT:
      ESP_LOGV(TAG, "BLE GAP SEC_REQ");
      // if(pDFault->DeBug){
      // sprintf(msgbuf, "BLE GAP SEC_REQ");
      // pmsgbx->dispMsg(msgbuf,TFT_WHITE);
      //}
      // Send the positive(true) security response to the peer device to accept the security request.
      // If not accept the security request, should send the security response with negative(false) accept value.
      esp_ble_gap_security_rsp(param->ble_security.ble_req.bd_addr, true);
      break;

    default:
      ESP_LOGV(TAG, "BLE GAP EVENT %s", ble_gap_evt_str(event));
      // if(pDFault->DeBug){
      // sprintf(msgbuf, "BLE GAP EVENT %s", ble_gap_evt_str(event));
      // pmsgbx->dispMsg(msgbuf,TFT_WHITE);
      //}
      break;
    }
  }
  //printf("ble_gap_event_handler EXIT\n"); //JMH Diagnosstic testing
} // jhm added this bracket
esp_err_t BTKeyboard::start_bt_scan(uint32_t seconds)
{
  esp_err_t ret = ESP_OK;
  if ((ret = esp_bt_gap_start_discovery(ESP_BT_INQ_MODE_GENERAL_INQUIRY, (int)(seconds / 1.28), 0)) != ESP_OK)
  {
    ESP_LOGE(TAG, "esp_bt_gap_start_discovery failed: %d", ret);
    if (pDFault->DeBug)
    {
      sprintf(msgbuf, "esp_bt_gap_start_discovery failed: %d", ret);
      pmsgbx->dispMsg(msgbuf, TFT_WHITE);
    }
    return ret;
  }
  return ret;
}

esp_err_t BTKeyboard::start_ble_scan(uint32_t seconds)
{
  static esp_ble_scan_params_t hid_scan_params = {
      .scan_type = BLE_SCAN_TYPE_ACTIVE,
      .own_addr_type = BLE_ADDR_TYPE_PUBLIC,
      .scan_filter_policy = BLE_SCAN_FILTER_ALLOW_ALL,
      .scan_interval = 0x50,
      .scan_window = 0x30,
      .scan_duplicate = BLE_SCAN_DUPLICATE_ENABLE,
  };

  esp_err_t ret = ESP_OK;
  if ((ret = esp_ble_gap_set_scan_params(&hid_scan_params)) != ESP_OK)
  {
    ESP_LOGE(TAG, "esp_ble_gap_set_scan_params failed: %d", ret);
    if (pDFault->DeBug)
    {
      sprintf(msgbuf, "esp_ble_gap_set_scan_params failed: %d", ret);
      pmsgbx->dispMsg(msgbuf, TFT_WHITE);
    }
    return ret;
  }
  WAIT_BLE_CB();

  if ((ret = esp_ble_gap_start_scanning(seconds)) != ESP_OK)
  {
    ESP_LOGE(TAG, "esp_ble_gap_start_scanning failed: %d", ret);
    if (pDFault->DeBug)
    {
      sprintf(msgbuf, "esp_ble_gap_start_scanning failed: %d", ret);
      pmsgbx->dispMsg(msgbuf, TFT_WHITE);
    }
    return ret;
  }
  return ret;
}

esp_err_t
BTKeyboard::esp_hid_scan(uint32_t seconds, size_t *num_results, esp_hid_scan_result_t **results)
{
  if (num_bt_scan_results || bt_scan_results || num_ble_scan_results || ble_scan_results)
  {
    ESP_LOGE(TAG, "There are old scan results. Free them first!");
    if (pDFault->DeBug)
    {
      sprintf(msgbuf, "There are old scan results. Free them first!");
      pmsgbx->dispMsg(msgbuf, TFT_WHITE);
    }
    return ESP_FAIL;
  }

  if (start_ble_scan(seconds) == ESP_OK)
  {
    WAIT_BLE_CB();
  }
  else
  {
    return ESP_FAIL;
  }

  if (start_bt_scan(seconds) == ESP_OK)
  {
    WAIT_BT_CB();
  }
  else
  {
    return ESP_FAIL;
  }

  *num_results = num_bt_scan_results + num_ble_scan_results;
  *results = bt_scan_results;

  if (num_bt_scan_results)
  {
    while (bt_scan_results->next != NULL)
    {
      bt_scan_results = bt_scan_results->next;
    }
    bt_scan_results->next = ble_scan_results;
  }
  else
  {
    *results = ble_scan_results;
  }

  num_bt_scan_results = 0;
  bt_scan_results = NULL;
  num_ble_scan_results = 0;
  ble_scan_results = NULL;

  return ESP_OK;
}
void BTKeyboard::devices_scan(int seconds_wait_time)
{
  size_t results_len = 0;
  esp_hid_scan_result_t *results = NULL;
 // bt_keyboard->OpnEvntFlg = false;
  ESP_LOGV(TAG, "SCAN...");
  sprintf(msgbuf, "Looking for Keyboard...\n");
  pmsgbx->dispMsg(msgbuf, TFT_YELLOW);

  // start scan for HID devices

  esp_hid_scan(seconds_wait_time, &results_len, &results);
  ESP_LOGV(TAG, "SCAN: %u results", results_len);
  if (results_len)
  {
    esp_hid_scan_result_t *r = results;
    esp_hid_scan_result_t *cr = NULL;
    while (r)
    {
      printf("%s: " ESP_BD_ADDR_STR ", ", (r->transport == ESP_HID_TRANSPORT_BLE) ? "BLE" : "BT ", ESP_BD_ADDR_HEX(r->bda));
      printf("RSSI: %d, ", r->rssi);
      printf("USAGE: %s, ", esp_hid_usage_str(r->usage));
      if (r->transport == ESP_HID_TRANSPORT_BLE)
      {
        cr = r;
        printf("APPEARANCE: 0x%04x, ", r->ble.appearance);
        printf("ADDR_TYPE: '%s', ", ble_addr_type_str(r->ble.addr_type));
      }
      if (r->transport == ESP_HID_TRANSPORT_BT)
      {
        cr = r;
        printf("COD: %s[", esp_hid_cod_major_str(r->bt.cod.major));
        esp_hid_cod_minor_print(r->bt.cod.minor, stdout);
        printf("] srv 0x%03x, ", r->bt.cod.service);
        print_uuid(&r->bt.uuid);
        printf(", ");
      }
      printf("NAME: %s ", r->name ? r->name : "");
      printf("\n");
      if (pDFault->DeBug)
      {
        sprintf(msgbuf, "NAME: %s\n", r->name ? r->name : "");
        pmsgbx->dispMsg(msgbuf, TFT_WHITE);
      }
      r = r->next;
    }
    
    if (cr != NULL)
    {
      // open the last result
      if((int)(cr->ble.addr_type) == 9536) bt_keyboard->Adc_Sw = 1;//classic bluetooth
      else{//ble
        bt_keyboard->Adc_Sw = 2;
        bt_keyboard->inPrgsFlg = true;
      }
      vTaskDelay(50/portTICK_PERIOD_MS);//pause long enough for flag change to take effect
      //sprintf(msgbuf, "Enter PAIRING code for %s\n", cr->name);
      //pmsgbx->dispMsg(msgbuf, TFT_GREEN);
      ESP_LOGI(TAG, "cr->ble.addr_type: %u\n", cr->ble.addr_type);
      bt_keyboard->ReConectFlg = true;
      dev = esp_hidh_dev_open(cr->bda, cr->transport, cr->ble.addr_type);// Returns immediately w/ BT classic device; But waits for pairing code w/ BLE device
      if (dev != NULL)
      {
        printf("esp_hidh_dev_open " ESP_BD_ADDR_STR " \n", ESP_BD_ADDR_HEX(cr->bda));
      }
      else{
        sprintf(msgbuf, "esp_hidh_dev_open failed\n");
        pmsgbx->dispMsg(msgbuf, TFT_YELLOW);
      }
      vTaskDelay(100/portTICK_PERIOD_MS);//pause long enough for flag change to take effect
      bt_keyboard->inPrgsFlg = false;}
    else
    {
      sprintf(msgbuf, "KeyBroard NOT found...\n");
      pmsgbx->dispMsg(msgbuf, TFT_YELLOW);
    }
    // free the results
    esp_hid_scan_results_free(results);
  }
  else
  {
    if (bt_keyboard->OpnEvntFlg)
    {
      sprintf(msgbuf, "Keyboard Ready...\n");
      pmsgbx->dispMsg(msgbuf, TFT_YELLOW);
    }
    else
    {
      sprintf(msgbuf, "NONE found...\n");
      pmsgbx->dispMsg(msgbuf, TFT_YELLOW);
    }
  }
}


void BTKeyboard::hidh_callback(void *handler_args, esp_event_base_t base, int32_t id, void *event_data)
{
  static const char *TAG1 = "hidh_callback";
  char temp[250];
  uint16_t clr = 0;
  temp[0] = 255;
  esp_hidh_event_t event = (esp_hidh_event_t)id;
  esp_hidh_event_data_t *param = (esp_hidh_event_data_t *)event_data;
  bool talk = false; //true;//false; //set to true for hid callback debugging //JMH Diagnosstic testing
  if (mutex != NULL)
  {
    /* See if we can obtain the semaphore.  If the semaphore is not
    available wait 15 ticks to see if it becomes free. */
    if (xSemaphoreTake(mutex, portMAX_DELAY) == pdTRUE) //(TickType_t)15
    {
      if(talk) printf("hidh_callback\n"); 
      switch (event)
      {
      case ESP_HIDH_OPEN_EVENT:
      {
        sprintf(temp, "ESP_HIDH_OPEN_EVENT\n");
        if (param->open.status == ESP_OK)
        {
          const uint8_t *bda = esp_hidh_dev_bda_get(param->open.dev);
          //ESP_LOGI(TAG, ESP_BD_ADDR_STR " OPEN: %s", ESP_BD_ADDR_HEX(bda), esp_hidh_dev_name_get(param->open.dev));
          ESP_LOGI(TAG, ESP_BD_ADDR_STR " OPEN: %s", ESP_BD_ADDR_HEX(bda), esp_hidh_dev_name_get(param->open.dev));
            esp_hidh_dev_dump(param->open.dev, stdout);
          /*Now go query the reports for this device/keyboard, & See if the Logictech 'F-Key' config report can be found*/
          /*JMH added the following to ferrit out Logitech keyboards*/
          /*Query the keyboard for reports*/
          
          if (talk)
          {
            printf("\n\nSTARTING REPORT REQUEST\n");
          }
          bool K380Fnd = false;
          int rptIndx = 0;
          size_t num_reports;
          esp_hid_report_map_t MyMap;

          ESP_ERROR_CHECK(esp_hidh_dev_reports_get(param->open.dev, &num_reports, &MyMap.reports));
          MyMap.reports_len = num_reports;
          if (talk)
          {
            sprintf(temp, "REPORT COUNT: %d\n", (int)num_reports);
            printf(temp);
          }
          /*see esp_hid_common.h for code definitions*/
          char typestr[10];
          char modestr[10];
          char usestr[14];
          for (int i = 0; i < MyMap.reports_len; i++)
          {
            if ((MyMap.reports[i].report_type == 0x2) && (MyMap.reports[i].report_id == 0x10 || MyMap.reports[i].report_id == 0x11) && (MyMap.reports[i].usage == 0x40))
            {
              rptIndx = i;
              K380Fnd = true;
            }

            /* for debugging print out reports found on the current device/keyboard*/
            /* decode the values returned*/
            switch (MyMap.reports[i].report_type)
            {
            case 1:
            {
              sprintf(typestr, "1 INPUT  ");
              break;
            }
            case 2:
            {
              sprintf(typestr, "2 OUTPUT ");
              break;
            }
            case 3:
            {
              sprintf(typestr, "3 FEATURE");
              break;
            }
            }
            switch (MyMap.reports[i].protocol_mode)
            {
            case 0:
            {
              sprintf(modestr, "0 BOOT  ");
              break;
            }
            case 1:
            {
              sprintf(modestr, "1 REPORT");
              break;
            }
            }
            switch (MyMap.reports[i].usage)
            {
            case 0:
            {
              sprintf(usestr, " 0 GENERIC ");
              break;
            }
            case 1:
            {
              sprintf(usestr, " 1 KEYBOARD");
              break;
            }
            case 2:
            {
              sprintf(usestr, " 2 MOUSE   ");
              break;
            }
            case 4:
            {
              sprintf(usestr, " 4 JOYSTICK");
              break;
            }
            case 8:
            {
              sprintf(usestr, " 8 GAMEPAD ");
              break;
            }
            case 16:
            {
              sprintf(usestr, "16 TABLET  ");
              break;
            }
            case 32:
            {
              sprintf(usestr, "32 CCONTROL");
              break;
            }
            case 64:
            {
              sprintf(usestr, "64 VENDOR  ");
              break;
            }
            }
            if (talk)
            {
              sprintf(temp, "| Map_Index %02x; Rpt_Id: %02x; Usage:%s; Type:%s; Mode%s; Rpt_len: %02d |\n",
                      MyMap.reports[i].map_index,
                      MyMap.reports[i].report_id,
                      usestr,
                      typestr,
                      modestr,
                      MyMap.reports[i].value_len);
              printf(temp);
            }
          }

          if (K380Fnd) // If true, we found a K380 Keyboard; Send command to reconfigure 'F' Keys
          {
            /*Logitech K380 Key Command*/
            uint8_t configKBrd[] = {0xff, 0x0b, 0x1e, 0x00, 0x00, 0x00};
            if (talk)
            {
              printf("K380 Key command: ");
              for (int i = 0; i < sizeof(configKBrd); i++)
              {
                sprintf(temp, "0x%02x:", configKBrd[i]); //
                printf(temp);
              }
              printf("\n\n");
            }
            ESP_ERROR_CHECK(esp_hidh_dev_output_set(param->open.dev, MyMap.reports[rptIndx].map_index, MyMap.reports[rptIndx].report_id, configKBrd, sizeof(configKBrd)));
            sprintf(temp, "K380 Found-Configured F-keys");
            // bt_keyboard->pmsgbx->dispMsg(temp, TFT_BLUE);
          }
          else
            sprintf(temp, "OPEN: %02x:%02x:%02x:%02x:%02x:%02x", ESP_BD_ADDR_HEX(bda));

          clr = TFT_GREEN;
          if(!bt_keyboard->OpnEvntFlg && !adcON){
            ESP_LOGI(TAG1, "adc_continuous_start");
            bt_keyboard->Adc_Sw = 2;
          }
          bt_keyboard->OpnEvntFlg = true;
          //bt_keyboard->pmsgbx->dispMsg("KEYBOARD READY\n", TFT_GREEN);
          
        }
        else
        {
          ESP_LOGE(TAG, " OPEN failed!");
        }
        break;
      }
      case ESP_HIDH_BATTERY_EVENT:
      {
        const uint8_t *bda = esp_hidh_dev_bda_get(param->battery.dev);
        ESP_LOGV(TAG, ESP_BD_ADDR_STR " BATTERY: %d%%", ESP_BD_ADDR_HEX(bda), param->battery.level);
        sprintf(temp, " BATTERY: %02x:%02x:%02x:%02x:%02x:%02x; %s", ESP_BD_ADDR_HEX(bda), esp_hidh_dev_name_get(param->open.dev));
        clr = TFT_YELLOW;
        bt_keyboard->set_battery_level(param->battery.level);
        break;
      }
      case ESP_HIDH_INPUT_EVENT:
      {
        const uint8_t *bda = esp_hidh_dev_bda_get(param->input.dev);
        ESP_LOGV("INPUT_EVENT", ESP_BD_ADDR_STR " INPUT: %8s, MAP: %2u, ID: %3u, Len: %d, Data:",
                 ESP_BD_ADDR_HEX(bda),
                 esp_hid_usage_str(param->input.usage),
                 param->input.map_index,
                 param->input.report_id,
                 param->input.length);
        char databuf[150];
        char databuf1[75];
        int cntr = 0;
        databuf1[0] =0;
        //const uint8_t indat = param->input.data;
        //unsigned int curdata[2];
        for(int i = 0; i<param->input.length; i++){
          //curdata[0] = (unsigned int )param->input.data[i];
          sprintf(databuf, "%s:%02x", databuf1, param->input.data[i]);
          if( param->input.data[i] == 0x01) cntr++;
          else cntr = 0;
          for(int p = 0; p<sizeof(databuf1); p++){
            databuf1[p] = databuf[p];
            if(databuf[p]==0) break;
          }
        }
        for(int p = 0; p<sizeof(databuf1); p++){
          databuf1[p] = databuf[p];
          if(databuf[p]==0) break;
        }
        if (talk){
          sprintf(temp, "INPUT_EVENT; ADDR:%02x:%02x:%02x:%02x:%02x:%02x; MAP:%s; NDX:%d; ID:%3u; LEN:%d; DATA%s\n",
                   ESP_BD_ADDR_HEX(bda),
                   esp_hid_usage_str(param->input.usage),
                   param->input.map_index,
                   param->input.report_id,
                   param->input.length,
                   databuf1);
        }
        clr = TFT_BLACK;                  
        ESP_LOG_BUFFER_HEX_LEVEL(TAG, param->input.data, param->input.length, ESP_LOG_DEBUG);
        if((cntr != 6) && !bt_keyboard->trapFlg){
          /*Classic BT Keybrds send key press date w/ data len = 8; K380s keybrd has a deta lenght of 7*/
          if(param->input.length == 8) bt_keyboard->push_key(param->input.data, param->input.length); // normal path when keystroke data is good/usuable
          else if(param->input.length == 7){// looks like K380s data. So add one additional data element (0) to the array
            uint8_t tmpdat[8];
            tmpdat[0] = param->input.data[0];
            tmpdat[1] = 0;
            for(int i =1; i< param->input.length; i++){
              tmpdat[i+1] = param->input.data[i];
            }
            bt_keyboard->push_key(tmpdat, 8);
          } 
        }
        else if(bt_keyboard->trapFlg){// path used to test for data corruption recovery 
          if(param->input.length == 1){
            bt_keyboard->trapFlg = false;
            
            bt_keyboard->pmsgbx->dispStat("KEYBOARD READY", TFT_GREEN);
            xSemaphoreGive(mutex);
            vTaskDelay(200/portTICK_PERIOD_MS);
            xSemaphoreTake(mutex, portMAX_DELAY);
          }
          break;
        } 
        else
        {
          /*Keybrd data is corrupt. So sit and wait while send buffer contents is completeS*/
          bt_keyboard->trapFlg = true;
          bt_keyboard->pmsgbx->dispStat("!!! KEYBOARD BLOCKED !!!", TFT_RED);
          if (talk)
          {
            printf("!!! DATA BLOCKED !!!\n");
          }
          xSemaphoreGive(mutex);//we're likely going to be stuck for awhile. So let the other parts of the program conitnue (i.e. send whats in the cw buffer)
          //while(clrbuf){
            vTaskDelay(200/portTICK_PERIOD_MS);
          //}
          if(talk) printf("WAITING FOR SOMETHING GOOD TO HAPPEN\n");
          xSemaphoreTake(mutex, portMAX_DELAY);
        }
        break;
      }
      case ESP_HIDH_FEATURE_EVENT:
      {
        const uint8_t *bda = esp_hidh_dev_bda_get(param->feature.dev);
        ESP_LOGV("FEATURE_EVENT", ESP_BD_ADDR_STR " FEATURE: %8s MAP: %2u, ID: %3u, Len: %d",
                 ESP_BD_ADDR_HEX(bda),
                 esp_hid_usage_str(param->feature.usage),
                 param->feature.map_index,
                 param->feature.report_id,
                 param->feature.length);
        ESP_LOG_BUFFER_HEX_LEVEL("FEATURE_EVENT", param->feature.data, param->feature.length, ESP_LOG_DEBUG);
        sprintf(temp, " FEATURE: %02x:%02x:%02x:%02x:%02x:%02x, MAP: %s, ID: %3u\n",
                ESP_BD_ADDR_HEX(bda),
                esp_hid_usage_str(param->feature.usage),
                param->feature.report_id); //,
                                           //(int)param->feature.length);
        // bt_keyboard->pmsgbx->dispMsg(temp, TFT_ORANGE);
        // temp[0] = 255;
        break;
      }
      case ESP_HIDH_CLOSE_EVENT:
      {
        const uint8_t *bda = esp_hidh_dev_bda_get(param->close.dev);
        ESP_LOGV(TAG, ESP_BD_ADDR_STR " CLOSE: %s", ESP_BD_ADDR_HEX(bda), esp_hidh_dev_name_get(param->close.dev));
        sprintf(temp, " CLOSE: %02x:%02x:%02x:%02x:%02x:%02x", ESP_BD_ADDR_HEX(bda));
        clr = TFT_RED;
        break;
      }
      default:
        ESP_LOGV(TAG, "**** UnHandled EVENT: %d\n", event);
        sprintf(temp, "UNHANDLED EVENT: %d\n", event);
        break;
      }
      if (temp[0] != 255)
      {
        /*took the post to display status line out because it could induce an unnecessary crash out because */
        if(clr != TFT_BLACK) bt_keyboard->pmsgbx->dispStat(temp, clr);
        if(talk) printf("hidh_callback EXIT: %s\n", temp); //JMH Diagnostic testing
        vTaskDelay(500/portTICK_PERIOD_MS);
      }
       
      xSemaphoreGive(mutex);
    }
  }
}

void BTKeyboard::push_key(uint8_t *keys, uint8_t size)
{
  
  KeyInfo inf;
  inf.modifier = (KeyModifier)keys[0];

  uint8_t max = (size > MAX_KEY_COUNT + 2) ? MAX_KEY_COUNT : size - 2;
  inf.keys[0] = inf.keys[1] = inf.keys[2] = 0;
  for (int i = 0; i < max; i++)
  {
    inf.keys[i] = keys[i + 2];
  }

  xQueueSend(event_queue, &inf, 0);
}

char BTKeyboard::wait_for_ascii_char(bool forever)
{
  KeyInfo inf;
  last_ch = 0;

  // printf( "**  wait_for_ascii_cha\n");//for testing/debugging
  while (true)
  {
    //repeat_period = pdMS_TO_TICKS(120);
    if (!wait_for_low_event(inf, (last_ch == 0) ? (forever ? portMAX_DELAY : 0) : repeat_period))
    {
      repeat_period = pdMS_TO_TICKS(120);
      return last_ch;
    }
    // printf( "**\n");
    int k = -1;
    for (int i = 0; i < MAX_KEY_COUNT; i++)
    {
      if ((k < 0) && key_avail[i])
        k = i;
      key_avail[i] = inf.keys[i] == 0;
    }

    if (k < 0)
    {
      continue;
    }

    char ch = inf.keys[k];
    /*JMH: uncomment the following to expose key entry values*/
    // char buf[20];
    // if((inf.keys[0] != (uint8_t)0) || (inf.keys[1] != (uint8_t)0) || (inf.keys[0] != (uint8_t)0) || ((uint8_t)inf.modifier != (uint8_t)0)){
    //    sprintf(buf, "%02x; %02x; %02x; %02x\n", inf.keys[0], inf.keys[1], inf.keys[2], (uint8_t)inf.modifier);
    //    printf(buf);//print to computer
    //    pmsgbx->dispMsg(buf, TFT_GOLD); //print to LCD Display
    // }
    /* special test for TAB */
    if (inf.keys[0] == 43 && ((uint8_t)inf.modifier == 0))
    {
      return last_ch = 0x97; // replace with up arrow
    }
    /* special test for Shift+TAB */
    if (inf.keys[0] == 43 && ((uint8_t)inf.modifier == 2))
    {
      return last_ch = 0x98; // replace with down arrow
    }
    /* special test for ctr+Enter */
    if ((inf.keys[1] == 0x28 || inf.keys[0] == 0x28) && ((uint8_t)inf.modifier == 1|| (uint8_t)inf.modifier == 16))
    {
      return last_ch = 0x9A;
    }
    /* special test for ctr+'T' */
    if (((uint8_t)inf.modifier == 1|| (uint8_t)inf.modifier == 16) && (inf.keys[1] == 23 || inf.keys[0] == 0x17))
    {
      return last_ch = 0x9B;
    }
    /* special test for ctr+'S' */
    if (((uint8_t)inf.modifier == 1|| (uint8_t)inf.modifier == 16) && (inf.keys[1] == 22 || inf.keys[0] == 0x16))
    {
      return last_ch = 0x9C;
    }
    /* special test for ctr+'f' */
    if (((uint8_t)inf.modifier == 1|| (uint8_t)inf.modifier == 16) && ((inf.keys[0] == 9) || (inf.keys[1] == 9)))
    {
      return last_ch = 0x9D;
    }
    /* special test for Left ctr+'d' */
    if (((uint8_t)inf.modifier == 1) && ((inf.keys[0] == 7) || (inf.keys[1] == 7)))
    {
      return last_ch = 0x9E;
    }
     /* special test for Left or Right ctr+'g' */
    if (((uint8_t)inf.modifier == 1|| (uint8_t)inf.modifier == 16) && ((inf.keys[0] == 10) || (inf.keys[1] == 10)))
    {
      return last_ch = 0xA1;
    }
    /* special test for Right ctr+'g' */
    if (((uint8_t)inf.modifier == 16) && (inf.keys[0] == 10))
    {
      return last_ch = 0xA2;
    }
    /* special test for ctr+'p' */
    if (((uint8_t)inf.modifier == 1|| (uint8_t)inf.modifier == 16) && ((inf.keys[0] == 0x13) || (inf.keys[1] == 0x13)))
    {
      return last_ch = 0x9F;
    }
    /* special test for Right ctr+'d' */
    if (((uint8_t)inf.modifier == 16) && (inf.keys[0] == 7))
    {
      return last_ch = 0xA0;
    }
    /* special test for 'del' */
    if (inf.keys[0] == 76 && ((uint8_t)inf.modifier == 0))
    {
      return last_ch = 0x2A;
    }
    if (ch >= 4)
    {
      if ((uint8_t)inf.modifier & CTRL_MASK)
      {
        if (ch < (3 + 26))
        {
          repeat_period = pdMS_TO_TICKS(500);
          return last_ch = (ch - 3);
        }
      }
      else if (ch <= 0x52)
      {
        // ESP_LOGI(TAG, "Scan code: %d", ch);
        if (ch == KEY_CAPS_LOCK) ch =0; //JMH Don't need or want "Caps lock" feature on CW keyboard
        // if (ch == KEY_CAPS_LOCK)
          //caps_lock = !caps_lock; //JMH Don't need or want "Caps lock" feature on CW keyboard
        if ((uint8_t)inf.modifier & SHIFT_MASK)
        {
          if (caps_lock)
          {
            repeat_period = pdMS_TO_TICKS(500);
            return last_ch = shift_trans_dict[(ch - 4) << 1];
          }
          else
          {
            repeat_period = pdMS_TO_TICKS(500);
            return last_ch = shift_trans_dict[((ch - 4) << 1) + 1];
          }
        }
        else
        {
          if (caps_lock)
          {
            repeat_period = pdMS_TO_TICKS(500);
            return last_ch = shift_trans_dict[((ch - 4) << 1) + 1];
          }
          else
          {
            repeat_period = pdMS_TO_TICKS(500);
            return last_ch = shift_trans_dict[(ch - 4) << 1];
          }
        }
      }
    }

    last_ch = 0;
  }
}
