jmharvey1/ESP32BtCWKeyBrd/src/TFTMsgBox.cpp

/*
 * TFTMsgBox.cpp
 *
 *  Created on: Oct 7, 2021
 *      Author: jim
 * 20230617 To support advanced DcodeCW "Bug" processes, reworked dispMsg2(void) to handle ASCII chacacter 0x8 "Backspace" symbol
 */
#include "TFTMsgBox.h"
#include "main.h"
#include "globals.h"
// #include "Arduino.h"//needed to support "delay()" function call

TFTMsgBox::TFTMsgBox(TFT_eSPI *tft_ptr, char *StrdTxt)
{
	ptft = tft_ptr;
	pStrdTxt = StrdTxt;
	txtpos = 0;
	RingbufPntr1 = 0;
	RingbufPntr2 = 0;
	CursorPntr = 0;
	cursorY = 0;
	cursorX = 0;
	cnt = 0; // used in scrollpage routine
	curRow = 0;
	offset = 0;
	oldstate =0;
	BlkState = false;
	SOTFlg = true;
	StrTxtFlg = false;
	ToneFlg = false;
	SpdFlg = false;
	Bump = false;
	PgScrld = false;
	BGHilite = false;
	ToneColor = 0;
};

void TFTMsgBox::InitDsplay(void)
{
	ptft->init(); // ptft->reset();
	ptft->setRotation(3); // valid values 1 or 3
	ptft->fillScreen(TFT_BLACK);
	ptft->fillScreen(TFT_BLACK); // have to call this twice, to ensure full erasure
	ptft->setCursor(cursorX, cursorY);
	ptft->setTextColor(TFT_WHITE); // tft.setTextColor(WHITE, BLACK);
	ptft->setTextSize(fontsize);		   // 2 for 320x480; 1 for 240x320
	ptft->setTextWrap(false);
};
/*Originally written to be called after returning from setup/settings screen*/
void TFTMsgBox::ReBldDsplay(void)
{
	if (xSemaphoreTake(mutex, pdMS_TO_TICKS(20)) == pdTRUE) // pdMS_TO_TICKS()//portMAX_DELAY
	{
		/* We were able to obtain the semaphore and can now access the
		shared resource. */
		mutexFLG = true;
		ptft->fillScreen(TFT_BLACK);
		/* We have finished accessing the shared resource.  Release the semaphore. */
		xSemaphoreGive(mutex);
		mutexFLG = false;
	}
	ReStrSettings();
	// char temp[50];
	// sprintf(temp, "%d;  %d;  %d;  %d; %d; %d", RingbufPntr1, RingbufPntr2, CursorPntr, cnt, curRow, offset);
	// printf(temp); // result of no entry: 35;  35;  40;  40; 1
	// printf("\n");
	//TODO this may need more thought
	RingbufPntr2 = 0;
	// if (!PgScrld) // the text entered has yet to fill the screen/display;	So we simply go back to the begining
	// {
	// 	RingbufPntr2 = 0;
	// }
	// else
	// {
	// 	RingbufPntr2 = RingbufPntr1 - RingBufSz;
	// 	if (RingbufPntr2 < 0)
	// 	{
	// 		int NegBuf2 = RingbufPntr2;
	// 		RingbufPntr2 = (RingBufSz + NegBuf2);
	// 	}
	// }
	/*reset pointers & counters*/
	cursorX = cursorY = curRow = cnt = offset = CursorPntr = 0;
	RingbufPntr1--;
	if(RingbufPntr1<0) RingbufPntr1 = RingBufSz-1;
	// sprintf(temp, "%d;  %d;  %d;  %d; %d", RingbufPntr1, RingbufPntr2, CursorPntr, cnt, curRow);
	// printf(temp); // result of no entry: 35;  35;  40;  40; 1
	// printf("\n");
	// delay(5000);
	Bump = true;
	bool curflg = SOTFlg;
	setSOTFlg(curflg); // one way to refresh the SOT/STR status box without having to reinvent the wheel
	while(RingbufPntr1 != RingbufPntr2){
		delay(1);
	}
	CursorPntr = StrdPntr;
}
/* normally called by the Keyboard parser process
 * the main feature of this entry point is to set
 * the cursor position pointer
 */
void TFTMsgBox::KBentry(char Ascii)
{
	char buf[2];
	uint16_t color = TFT_WHITE;
	buf[0] = Ascii;
	buf[1] = 0;

	if (StrTxtFlg)
	{
		pStrdTxt[txtpos] = Ascii;
		pStrdTxt[txtpos + 1] = 0;
		txtpos++;
		if (txtpos >= 19)
			txtpos = 18;
		else
			color = TFT_YELLOW;
	}
	if (CursorPntr == 0)
		CursorPntr = cnt;
	dispMsg(buf, TFT_WHITE);
};
void TFTMsgBox::dispMsg(char Msgbuf[50], uint16_t Color)
{
	int msgpntr = 0;
	
	/* Add the contents of the Msgbuf to ringbuffer */

	while (Msgbuf[msgpntr] != 0)
	{
		if (RingbufPntr1 < RingBufSz - 1)
			RingbufChar[RingbufPntr1 + 1] = 0;
		else
			RingbufChar[0] = 0;
		RingbufChar[RingbufPntr1] = Msgbuf[msgpntr];
		RingbufClr[RingbufPntr1] = Color;
		RingbufPntr1++;
		if (RingbufPntr1 == RingBufSz)
			RingbufPntr1 = 0;
		msgpntr++;
		/*Added the following lines to maintain sync of the keyboard cursor as new characters are added to the screen via the CW decoder process*/
		if(Color == TFT_GREENYELLOW){
			if(CursorPntr < cnt+1) CursorPntr = cnt+1;
			// char buf[30];
			// sprintf(buf, "CrsrPntr: %d; cnt: %d\r\n", CursorPntr, cnt);
			// printf(buf);
		}
	}
};
/* timer interrupt driven method. drives the Ringbuffer pointer to ensure that
 * character(s) sent to TFT Display actually get printed (when time permits)X WPM & RX Tone Strenght/color 
 */
void TFTMsgBox::dispMsg2(void)
{
	//char buf[2];
	// char PrntBuf[20];
	/*For debugging */
	// buf[1] = 0;
	// if(RingbufPntr2 != RingbufPntr1) printf( "**");
	if (ToneFlg)
	{
		ToneFlg = false;
		int Wdth = 15;
		int Hght = 15;
		ptft->fillRect(StusBxX - 15, StusBxY + 10, Wdth, Hght, ToneColor);
	}
	if (SpdFlg)
	{
		SpdFlg = false;
		dispStat(SpdBuf, SpdClr);
	}
	while (RingbufPntr2 != RingbufPntr1)
	{
		/*test if this next entry is going to generate a scroll page event
		& are we in the middle of sending a letter; if true, skip this update.
		This was done to fix an issue with the esp32 & not being able to give the dotclock ISR
		priority over the display ISR */
		if (CWActv && (((cnt + 1) - offset) * fontW >= displayW) && (curRow + 1 == row))
		{
			// char buf[50];
			// sprintf(buf, "currow: %d; row: %d", curRow, row);
			// dispStat(buf, TFT_GREENYELLOW);//update status line
			// setSOTFlg(false);//changes status square to yellow
			break;
		}
		ptft->setCursor(cursorX, cursorY);
		char curChar = RingbufChar[RingbufPntr2];
		if(curChar == 0x8 ) // test for "Backspace", AKA delete ASCII symbol
		{
			Delete(1);
		}
		else if (curChar == 10){// test for "line feed" character
		
			DisplCrLf();
			// printf("cnt:%d; \n", cnt);
		
		}
		else // at this point, whatever is left shoud be regular text
		{
			uint16_t Color = RingbufClr[RingbufPntr2]; 
			ptft->setTextColor(RingbufClr[RingbufPntr2]);
			// sprintf(buf, "%s",curChar);
			// printf(buf);
			ptft->print(curChar);
			/* If needed add this character to the Pgbuf */
			if (curRow > 0)
			{
				Pgbuf[cnt - CPL] = curChar;
				Pgbuf[cnt - (CPL - 1)] = 0;
				PgbufColor[cnt - CPL] = Color;
			}
			cnt++;
			// printf("cnt:%d; ", cnt);
			if ((cnt - offset) * fontW >= displayW)
			{
				curRow++;
				cursorX = 0;
				cursorY = curRow * (fontH);
				offset = cnt;
				ptft->setCursor(cursorX, cursorY);
				if (curRow + 1 > row)
				{
					scrollpg();
				}
			}
			else
			{
				cursorX = (cnt - offset) * fontW;
			}
		}
		
		RingbufPntr2++;
		if (RingbufPntr2 == RingBufSz)
			RingbufPntr2 = 0;
	} // End while loop
	if (Bump)
	{
		Bump = false;
		RingbufPntr1++;
		if (RingbufPntr1 == RingBufSz)
			RingbufPntr1 = 0;
		dispStat(LastStatus, LastStatClr);
	}
	int blks = BlkStateCntr;
	while (BlkStateCntr > 0)
	{
		IntrCrsr(BlkStateVal[blks - BlkStateCntr]);
		BlkStateCntr--;
	}
};
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
